PTBresearch/Grover-Demonstrator/arduino-code/probabilities.h

#include <Arduino.h>
#include <avr/pgmspace.h>

const uint16_t probabilities[3][13][64] PROGMEM = {
  // Ideal Simulation
  {
    {   64,   57,   71,   65,   67,   62,   72,   71,   68,   62,   55,   69,   73,   68,   71,   70,   69,   70,   54,   58,   59,   63,   66,   78,   72,   65,   61,   59,   76,   56,   59,   67,   66,   53,   64,   75,   56,   72,   54,   60,   66,   60,   51,   68,   63,   64,   65,   62,   64,   50,   53,   62,   63,   59,   56,   63,   74,   77,   67,   64,   45,   83,   66,   54 },
    {   45,   73,   72,   54,   60,   56,   55,   58,   44,   46,   61,   48,   72,   52,   53,   63,   56,   57,   60,   61,   56,  540,   56,   64,   63,   46,   52,   54,   40,   54,   60,   63,   56,   52,   61,   63,   45,   52,   49,   53,   47,   51,   51,   42,   57,   45,   62,   54,   51,   65,   57,   50,   53,   61,   66,   76,   79,   58,   55,   55,   56,   57,   70,   53 },
    {   47,   43,   29,   56,   45,   48,   43,   43,   31,   47,   38,   38,   38,   46,   39,   34,   47,   46,   41,   43,   51, 1375,   49,   41,   39,   46,   34,   46,   56,   50,   38,   49,   43,   41,   35,   42,   43,   31,   39,   30,   50,   43,   44,   65,   50,   41,   34,   52,   38,   40,   51,   39,   38,   53,   44,   37,   46,   52,   43,   49,   39,   49,   40,   39 },
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

  }
};
